MaxJ02/Death_By_Table/Styrsystem/styrsystem/pid.cpp

/********************************************************************************
* pid.c: Contains drivers for user friendly PID controllers.
********************************************************************************/
#include "header.hpp"

/* Static functions: */
static inline void pid_check_output(struct pid* self);

/********************************************************************************
* pid_init: Initiates PID controller with specified parameters.
*
*           - self      : Reference to the PID controller.
*           - target    : Desired output value.
*           - output_min: Minimum output value.
*           - output_max: Maximum output value .
*           - kp        : Proportional constant.
*           - ki        : Integrate constant.
*           - kd        : Derivate constant.
********************************************************************************/
void pid_init(struct pid* self,
              const double target,
              const double output_min,
              const double output_max,
              const double kp,
              const double ki,
              const double kd)
{
   self->target = target;
   self->output_min = output_min;
   self->output_max = output_max;
   self->kp = kp;
   self->ki = ki;
   self->kd = kd;

   self->output = 0;
   self->input = 0;
   self->last_error = 0;
   self->integrate = 0;
   self->derivate = 0;
   return;
}

/********************************************************************************
* pid_regulate: Regulates output value of PID controller on the basis of
*               specified new input value.
*
*               - self     : Reference to the PID controller.
*               - new_input: New input value of PID controller.
********************************************************************************/
void pid_regulate(struct pid* self,
                  const double new_input)
{
   const double error = self->target - new_input;
   self->input = new_input;

   self->derivate = error - self->last_error;
   self->integrate += error;
   self->output = self->target + self->kp * error + 
                  self->ki * self->integrate + 
                  self->kd * self->derivate;

   pid_check_output(self);
   self->last_error = error;
   return;
}

/********************************************************************************
* pid_check_output: Checks if the PID controller output value is within
*                   specified minimum and maximum output value. If the output
*                   value is out of this range, the value is set to nearest
*                   boundary.
*
*                   - self: Reference to the PID controller.
********************************************************************************/
static inline void pid_check_output(struct pid* self)
{
   if (self->output < self->output_min)
   {
      self->output = self->output_min;
   }
   else if (self->output > self->output_max)
   {
      self->output = self->output_max;
   }
   return;
}

/********************************************************************************
* set_pid: Sets new pid values.
********************************************************************************/
void set_pid(struct pid* self, double kp, double ki, double kd)
{
  self->kp = kp;
  self->ki = ki;
  self->kd = kd;
  return;
}
